LobinArcolungo/Remo-te/photos/12V3A_power_supply.jpg

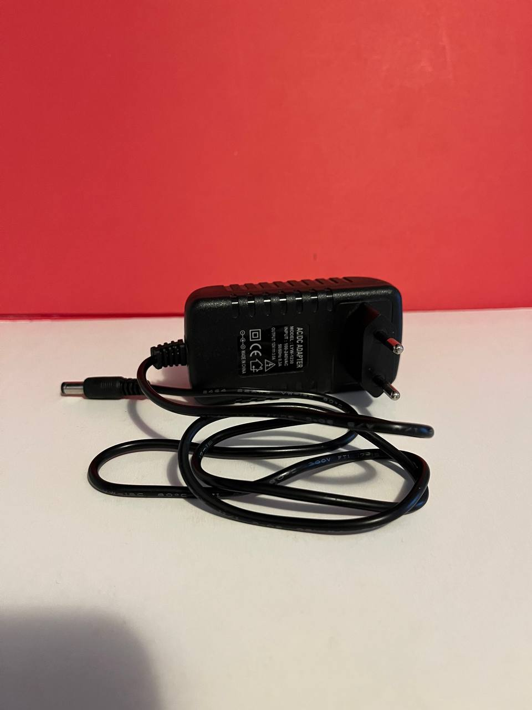
photos/12V3A_power_supply.jpg
