LobinArcolungo/Remo-te/photos/bearing_housing.jpg

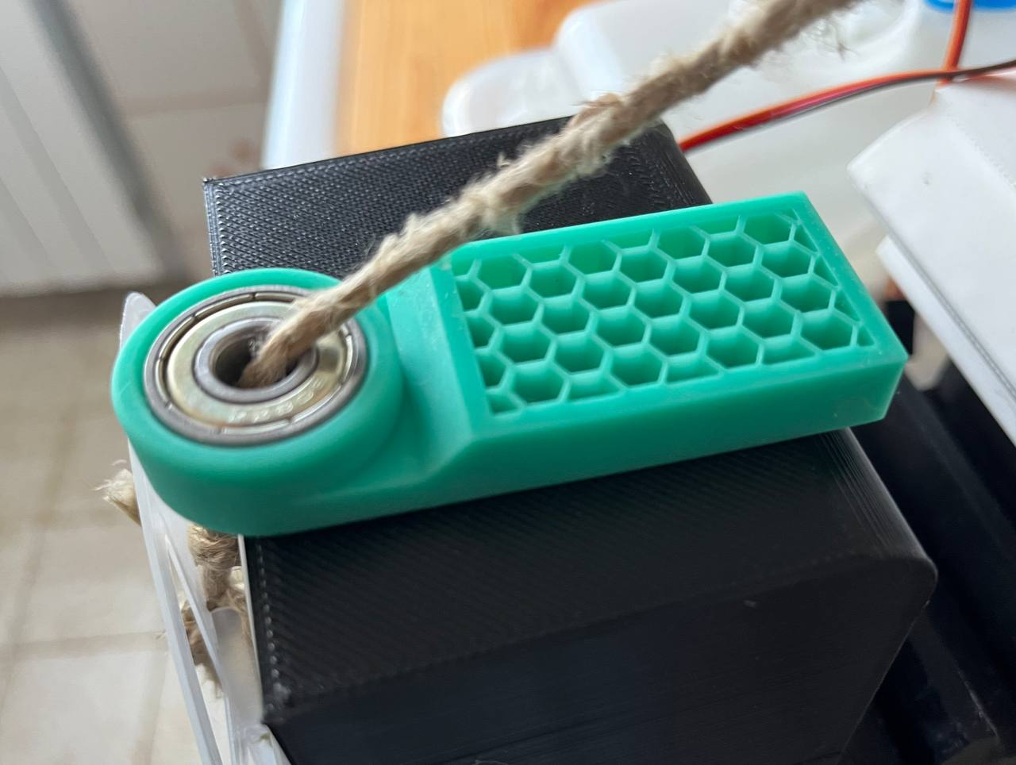
photos/bearing_housing.jpg
