LobinArcolungo/Remo-te/photos/boiler.jpg

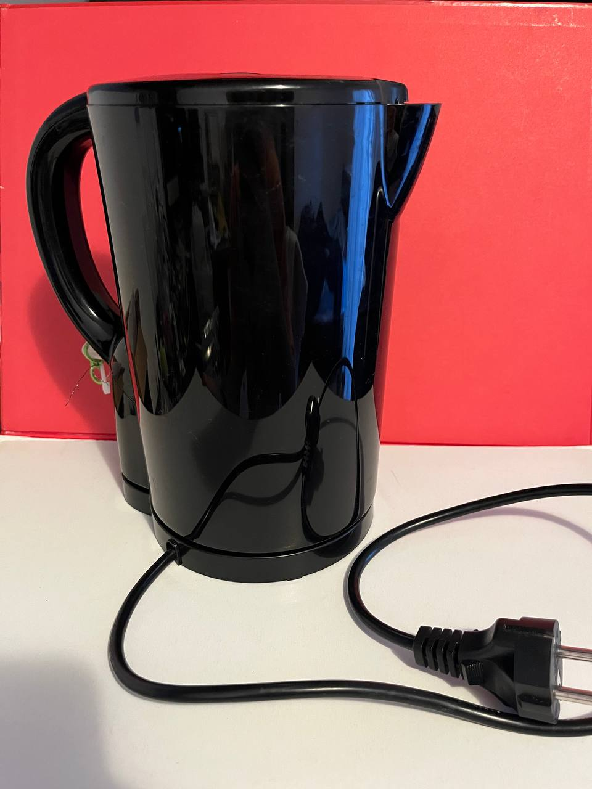
photos/boiler.jpg
