LobinArcolungo/Remo-te/photos/dock_front.jpg

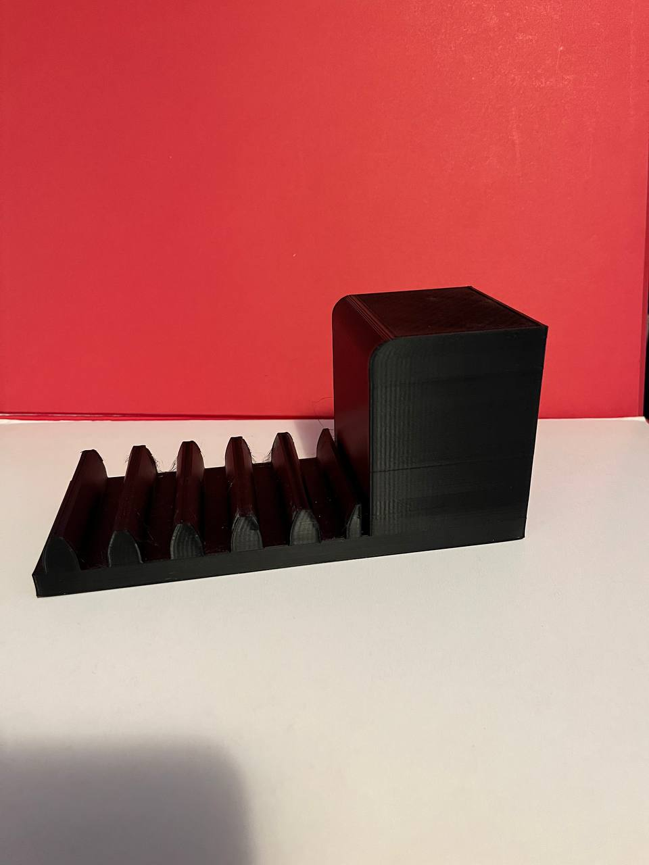
photos/dock_front.jpg
