LobinArcolungo/Remo-te/photos/servo.jpg

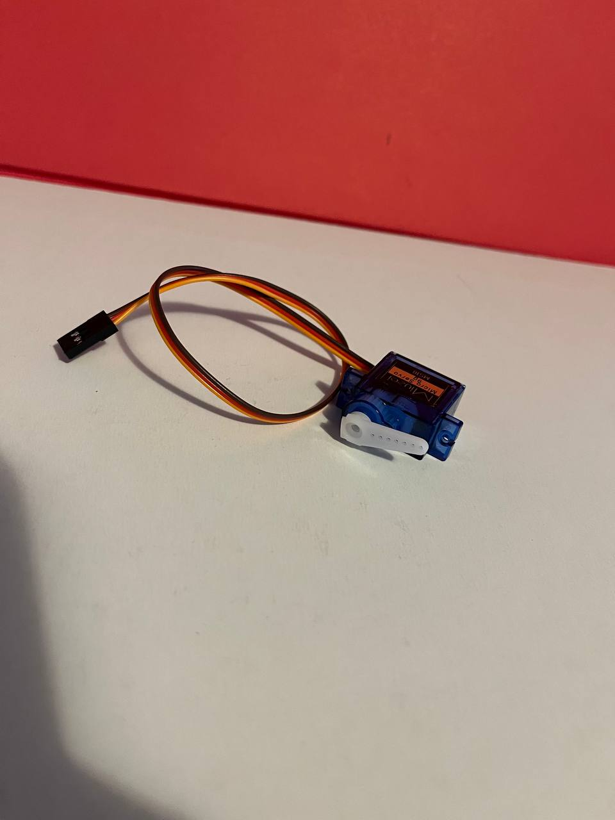
photos/servo.jpg
