LobinArcolungo/Remo-te/photos/stepper_motor_pulley_above.jpg

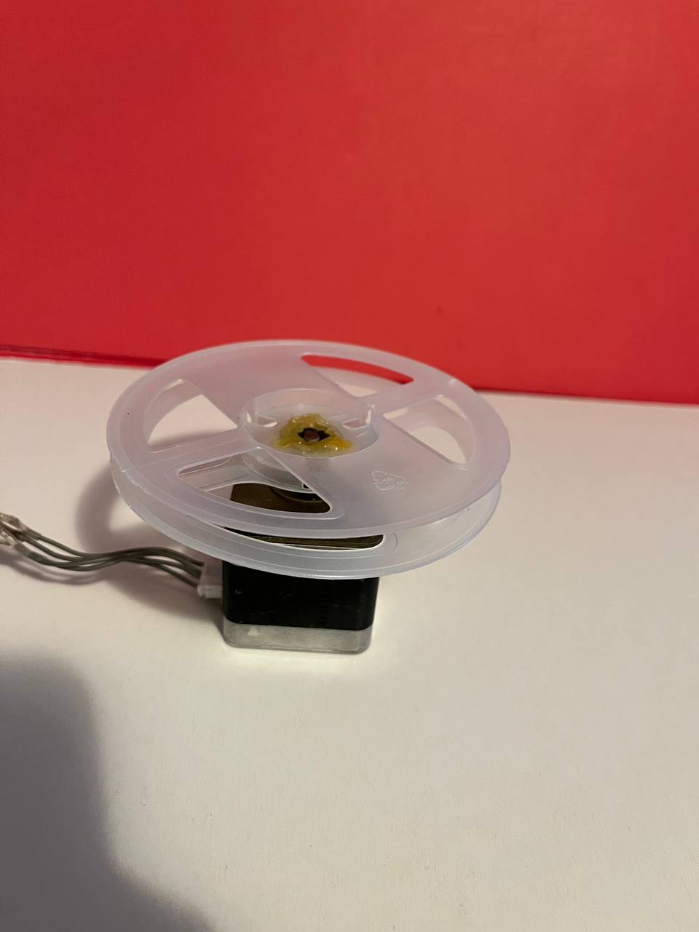
photos/stepper_motor_pulley_above.jpg
