LobinArcolungo/Remo-te/photos/stepper_motor_pulley_angle.jpg

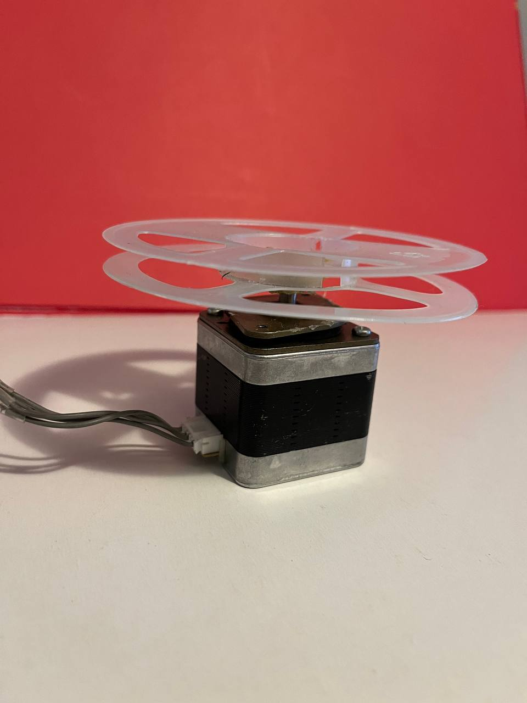
photos/stepper_motor_pulley_angle.jpg
