LobinArcolungo/Remo-te/photos/stepper_motor_pulley_side.jpg

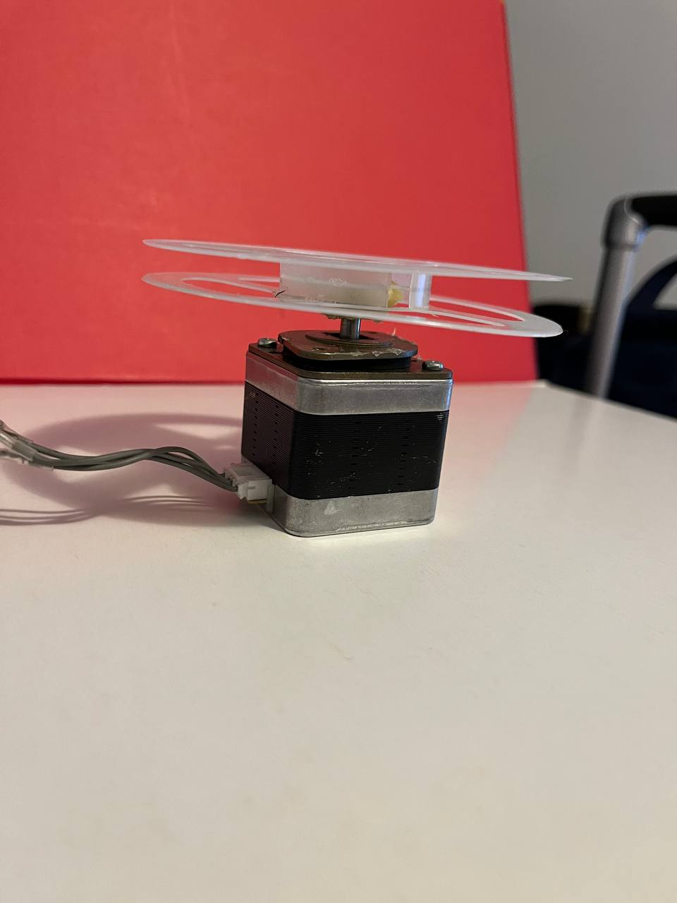
photos/stepper_motor_pulley_side.jpg
