LobinArcolungo/Remo-te/photos/triple_plug.jpg

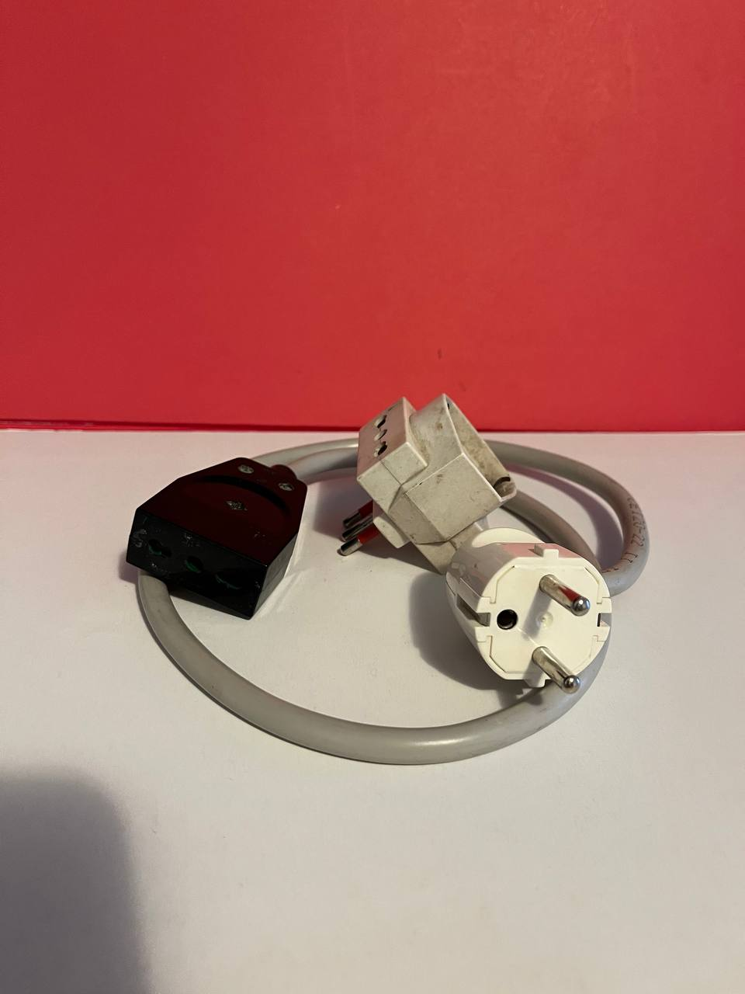
photos/triple_plug.jpg
