LobinArcolungo/Remo-te/photos/turning_on_mechanism.jpg

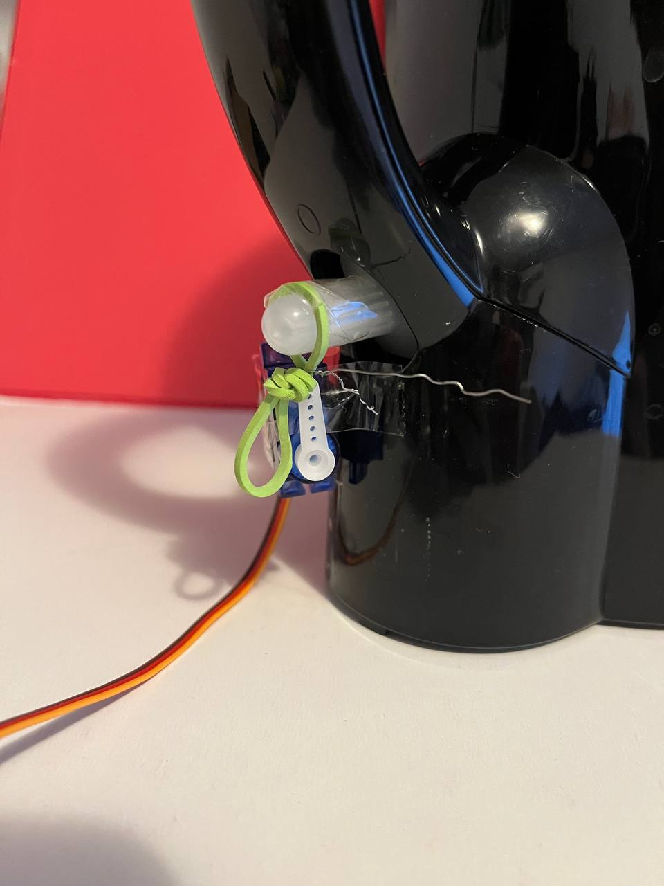
photos/turning_on_mechanism.jpg
