LobinArcolungo/Remo-te/photos/twine_and_bearing.jpg

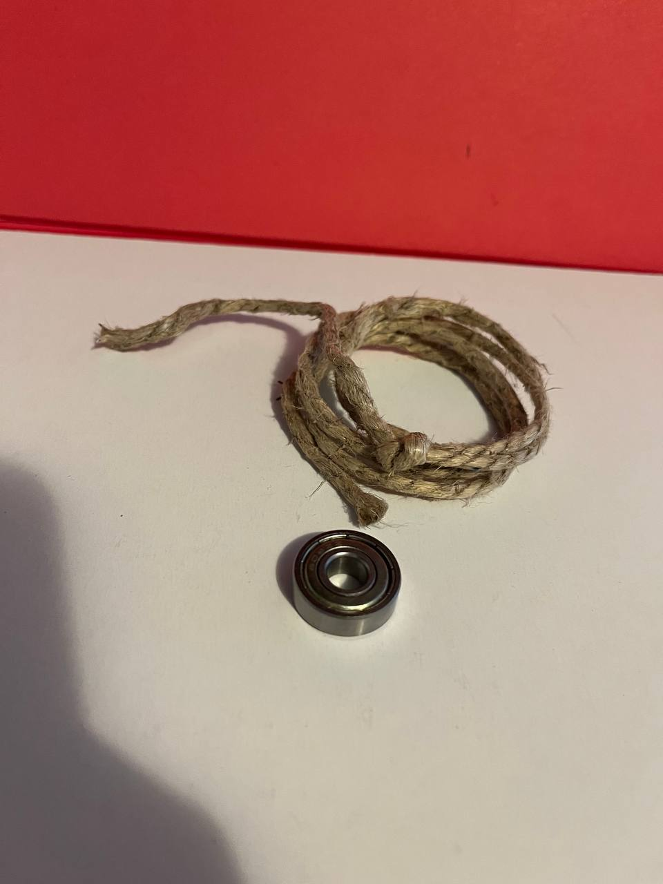
photos/twine_and_bearing.jpg
