LobinArcolungo/Remo-te/circuit_history/circuit_Remo_te_v3.png

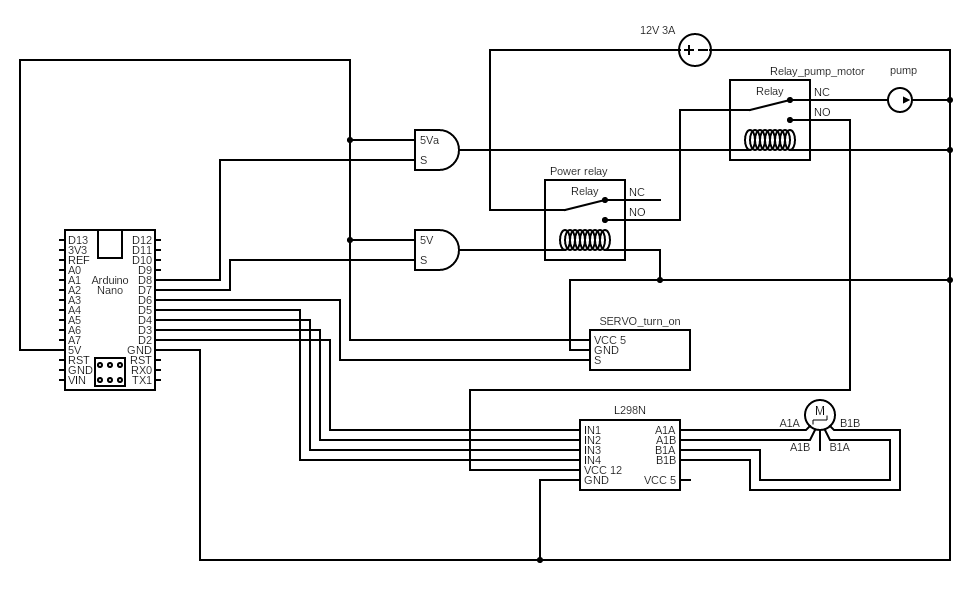
circuit_history/circuit_Remo_te_v3.png
