LobinArcolungo/Remo-te/circuit_history/circuit_Remo_te_v6_ESP.png

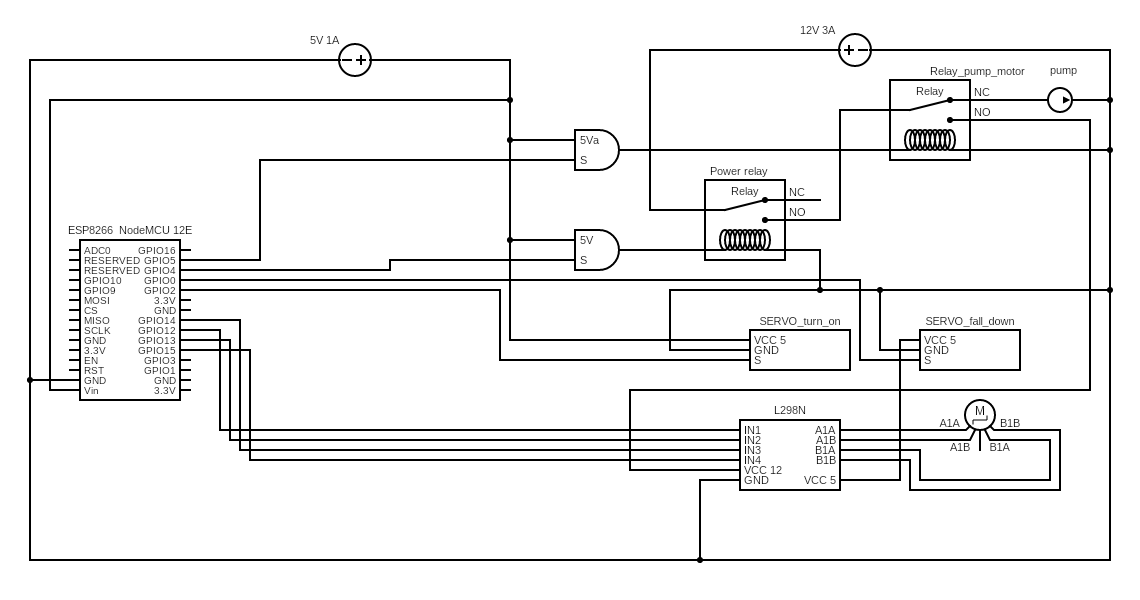
circuit_history/circuit_Remo_te_v6_ESP.png
