LobinArcolungo/Remo-te/circuit_history/circuit_Remo_te_v8_ESP_commond_ground_after.png

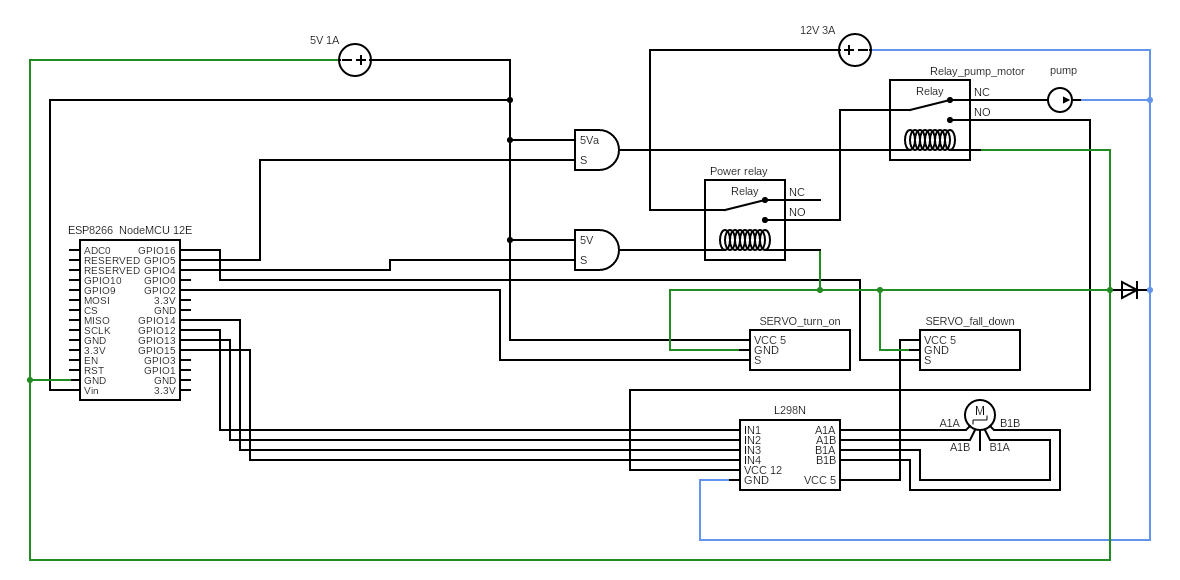
circuit_history/circuit_Remo_te_v8_ESP_commond_ground_after.png
