LobinArcolungo/Remo-te/circuit_history/circuit_Remo_te_v11_esp_nano.png

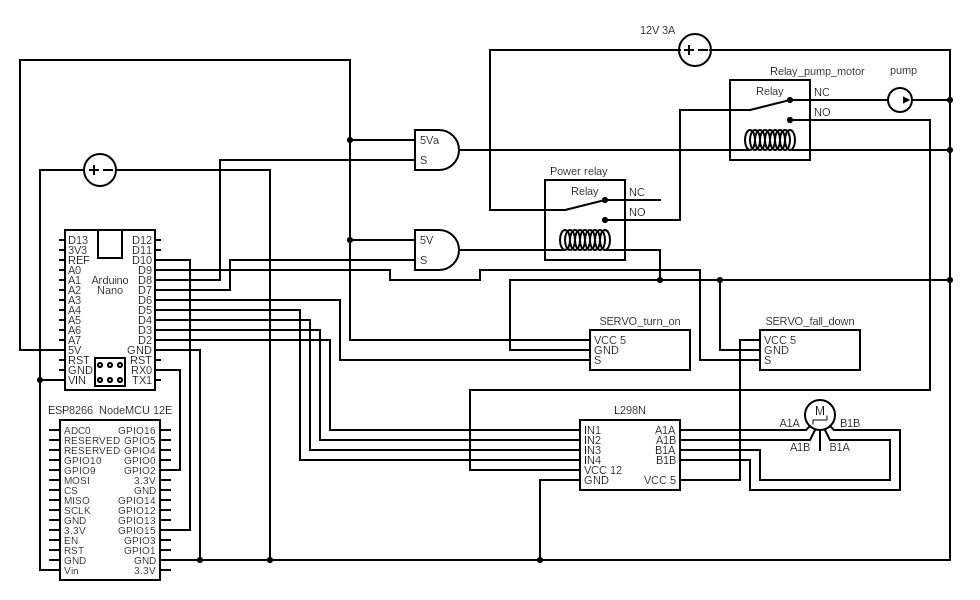
circuit_history/circuit_Remo_te_v11_esp_nano.png
